CedarGroveStudios/Robot_Friend_FeatherWing/code/RobotFriend_tiny.bmp

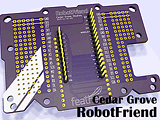
code/RobotFriend_tiny.bmp
