CedarGroveStudios/Robot_Friend_FeatherWing/photos and graphics/9mm_board_spacers.jpg

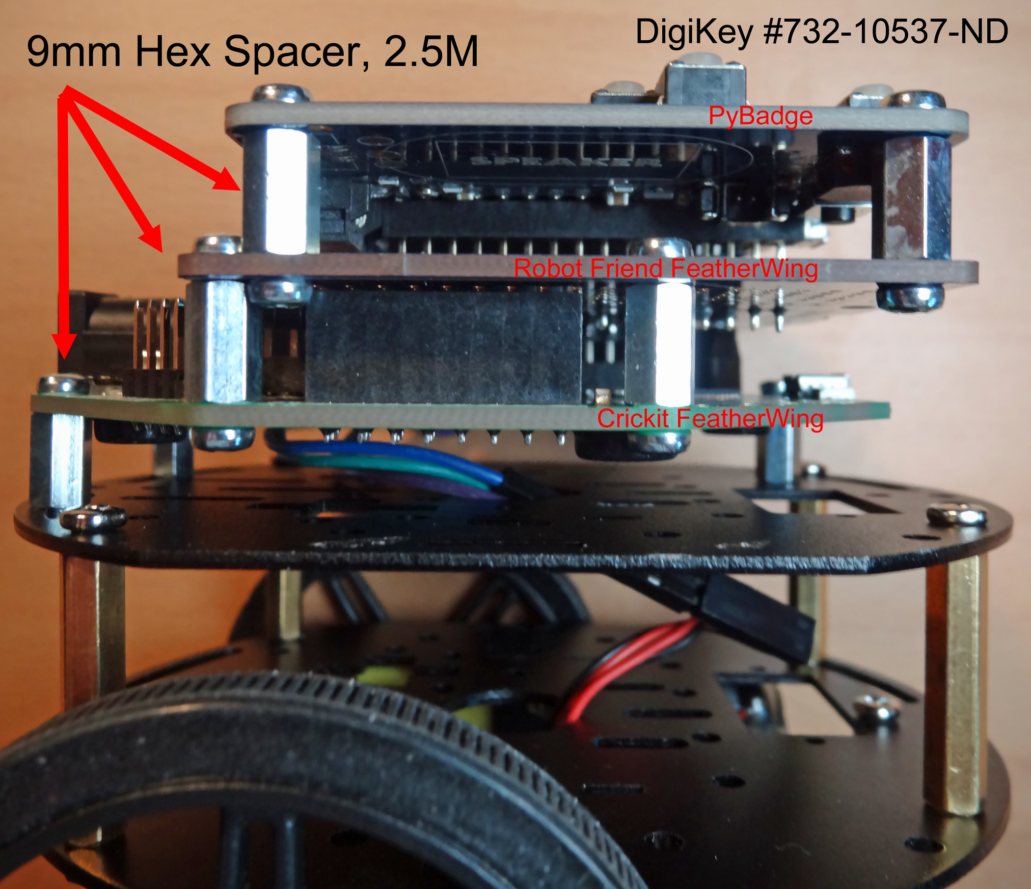
photos and graphics/9mm_board_spacers.jpg
