CedarGroveStudios/Robot_Friend_FeatherWing/photos and graphics/9mm_board_spacers_wide.jpg

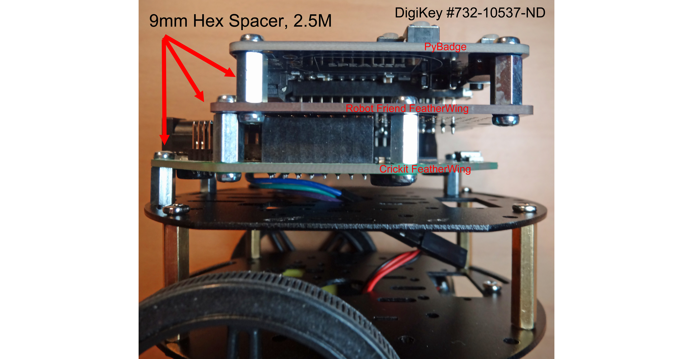
photos and graphics/9mm_board_spacers_wide.jpg
