CedarGroveStudios/Robot_Friend_FeatherWing/photos and graphics/2019-12-12_stemma_discovery.jpg

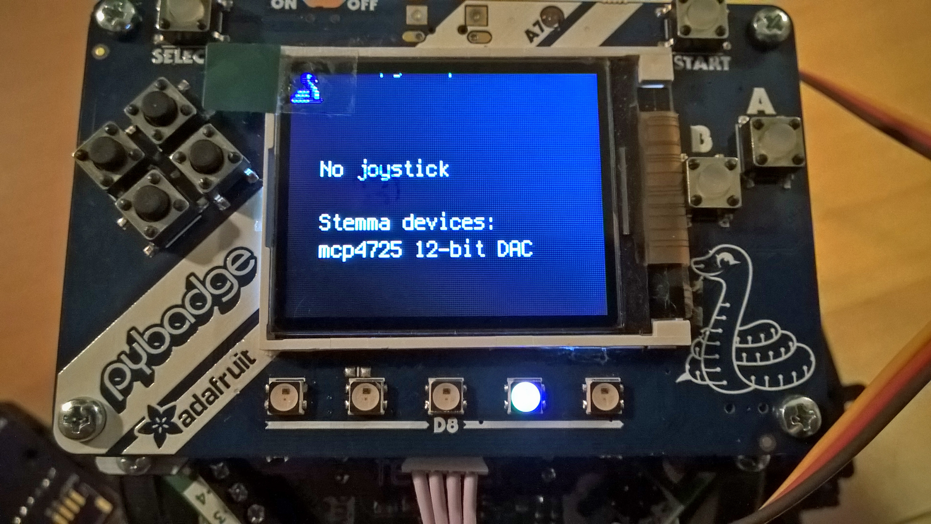
photos and graphics/2019-12-12_stemma_discovery.jpg
