CedarGroveStudios/Robot_Friend_FeatherWing/photos and graphics/Crickit_audio_jumper.jpg

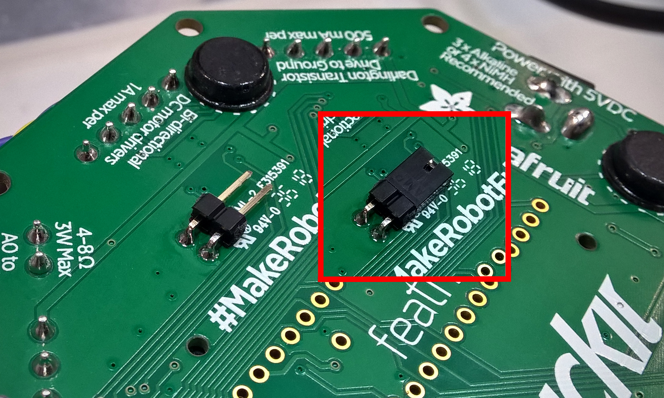
photos and graphics/Crickit_audio_jumper.jpg
