CedarGroveStudios/Robot_Friend_FeatherWing/photos and graphics/DSC05847a.jpg

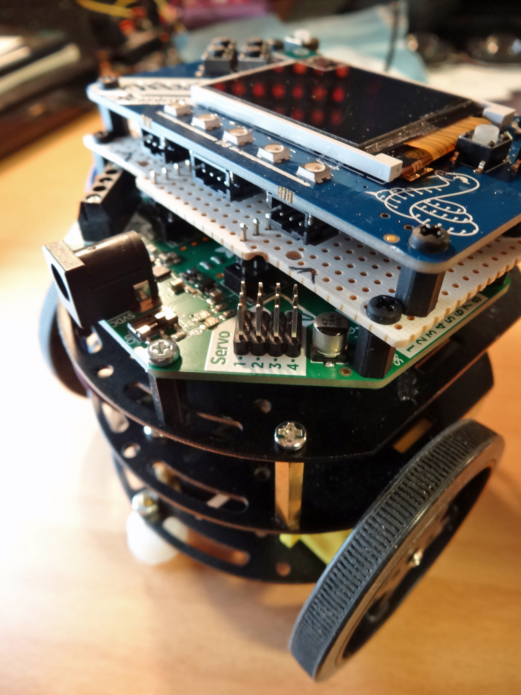
photos and graphics/DSC05847a.jpg
