CedarGroveStudios/Robot_Friend_FeatherWing/photos and graphics/DSC05849a.jpg

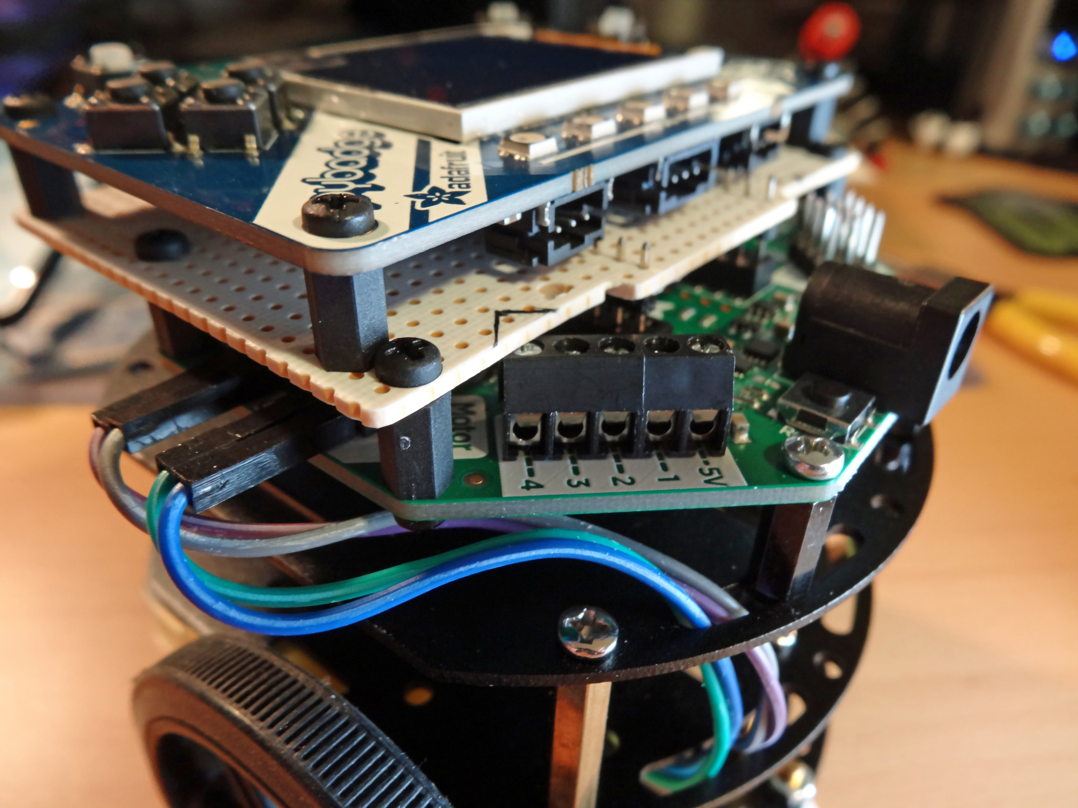
photos and graphics/DSC05849a.jpg
