CedarGroveStudios/Robot_Friend_FeatherWing/photos and graphics/DSC05850a.jpg

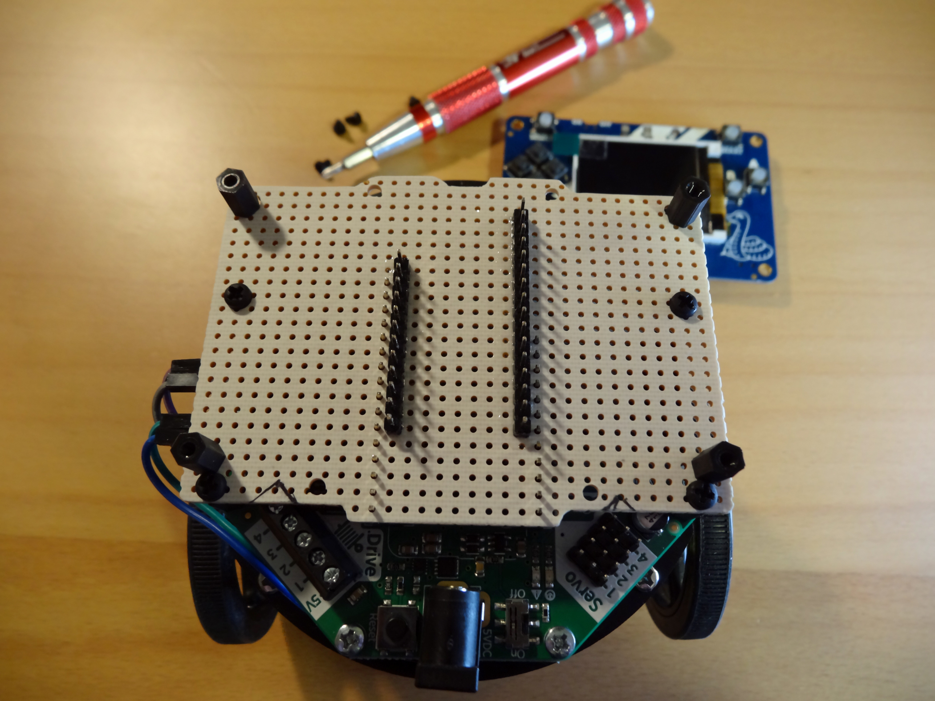
photos and graphics/DSC05850a.jpg
