CedarGroveStudios/Robot_Friend_FeatherWing/photos and graphics/DSC05886a.jpg

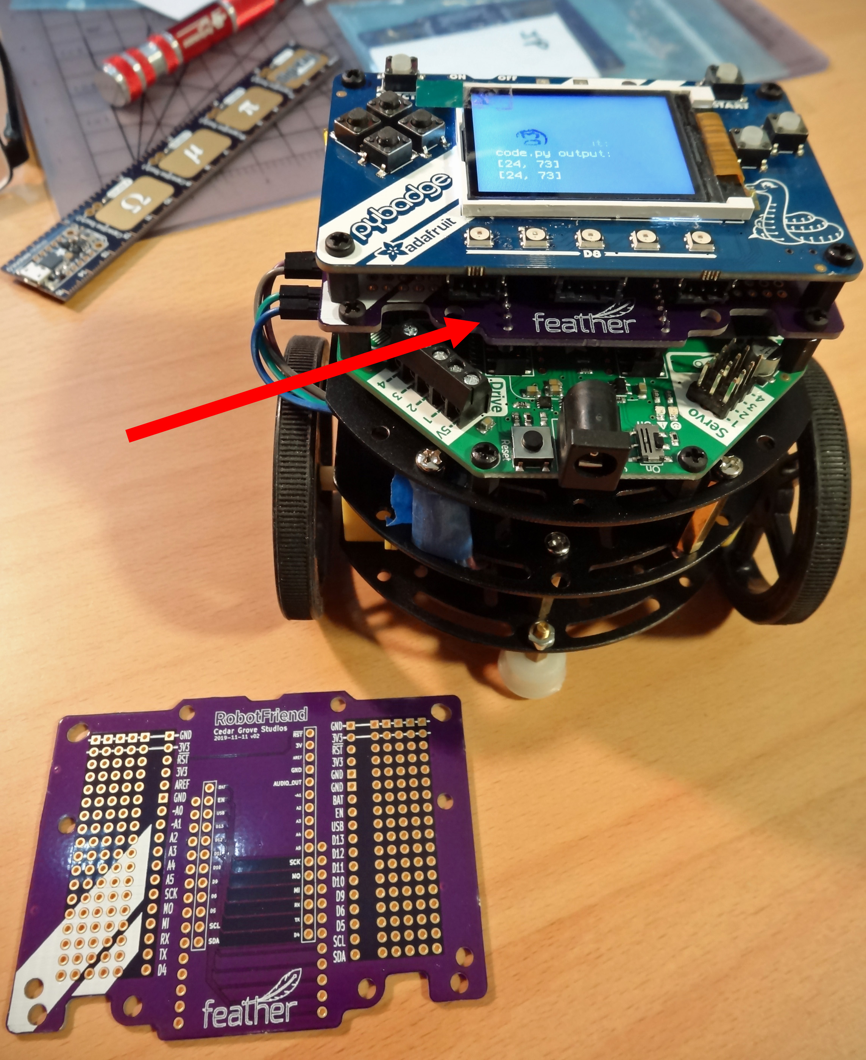
photos and graphics/DSC05886a.jpg
