CedarGroveStudios/Robot_Friend_FeatherWing/photos and graphics/DSC05920a lores.jpg

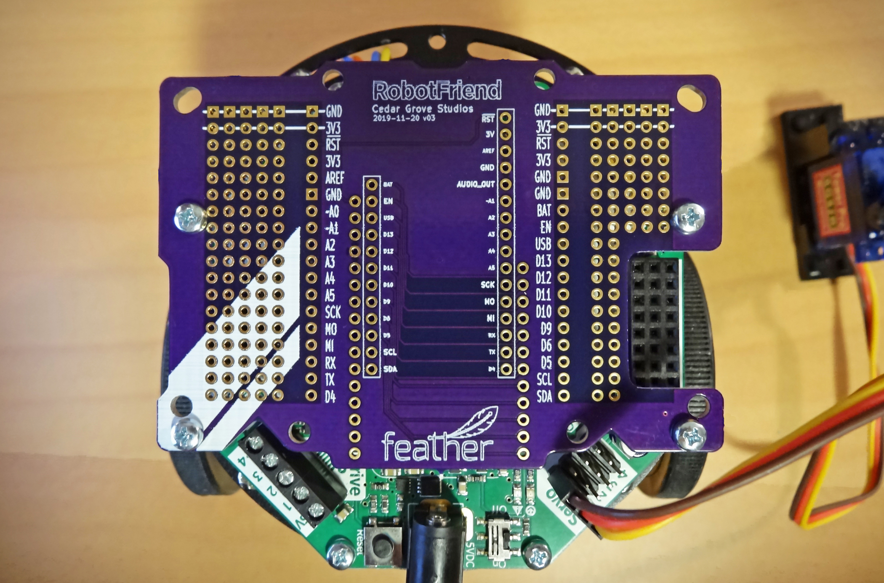
photos and graphics/DSC05920a lores.jpg
