CedarGroveStudios/Robot_Friend_FeatherWing/photos and graphics/musique concrete/DSC05933.JPG

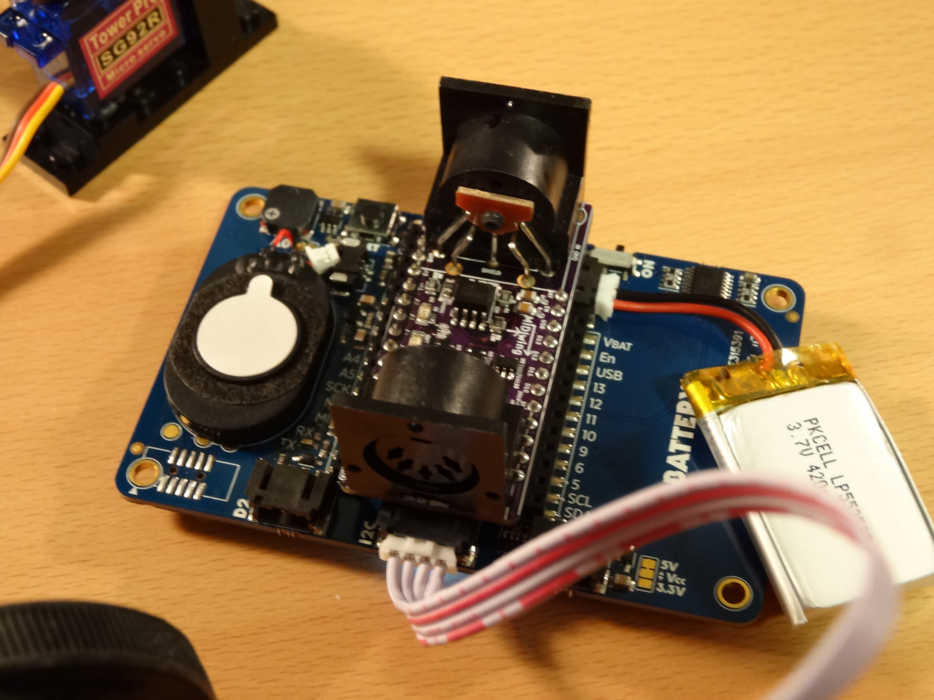
photos and graphics/musique concrete/DSC05933.JPG
