CedarGroveStudios/Robot_Friend_FeatherWing/photos and graphics/musique concrete/DSC05933a.jpg

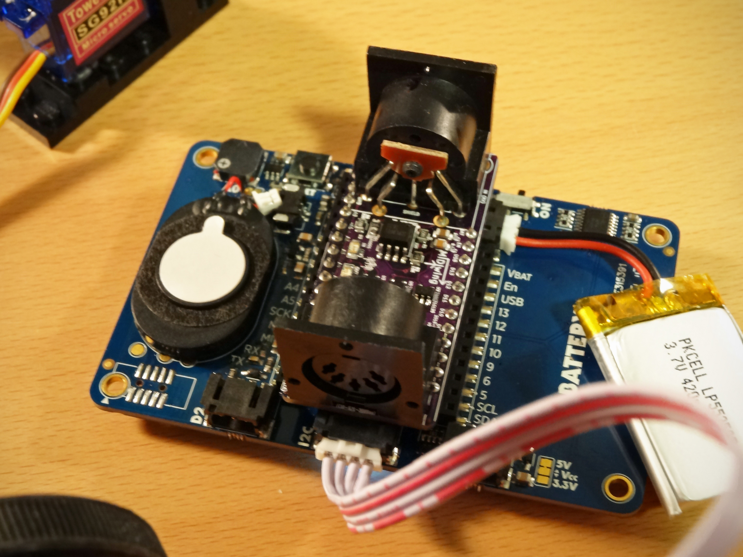
photos and graphics/musique concrete/DSC05933a.jpg
