CedarGroveStudios/Robot_Friend_FeatherWing/photos and graphics/musique concrete/DSC05934.JPG

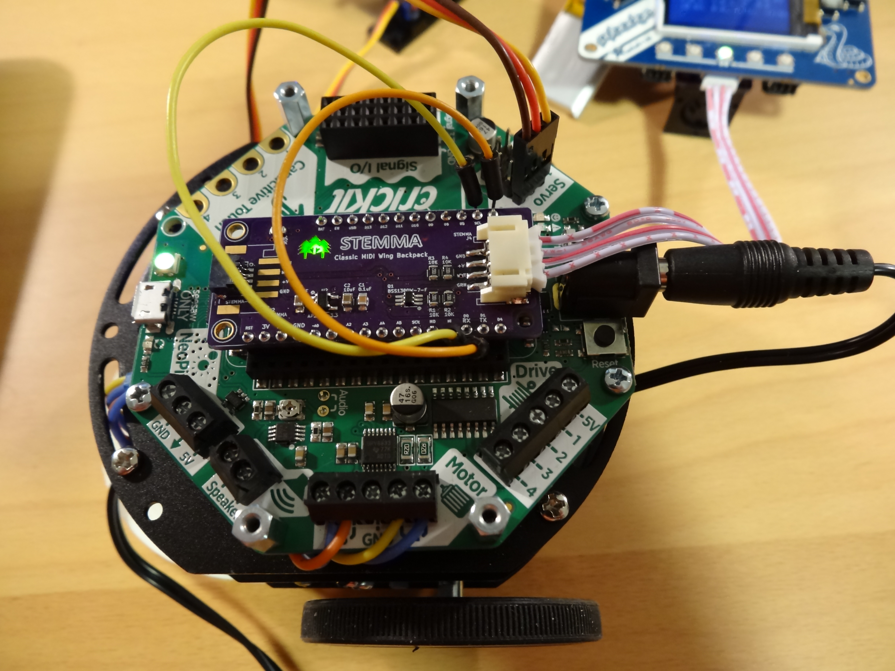
photos and graphics/musique concrete/DSC05934.JPG
