CedarGroveStudios/Robot_Friend_FeatherWing/photos and graphics/musique concrete/DSC05934a.jpg

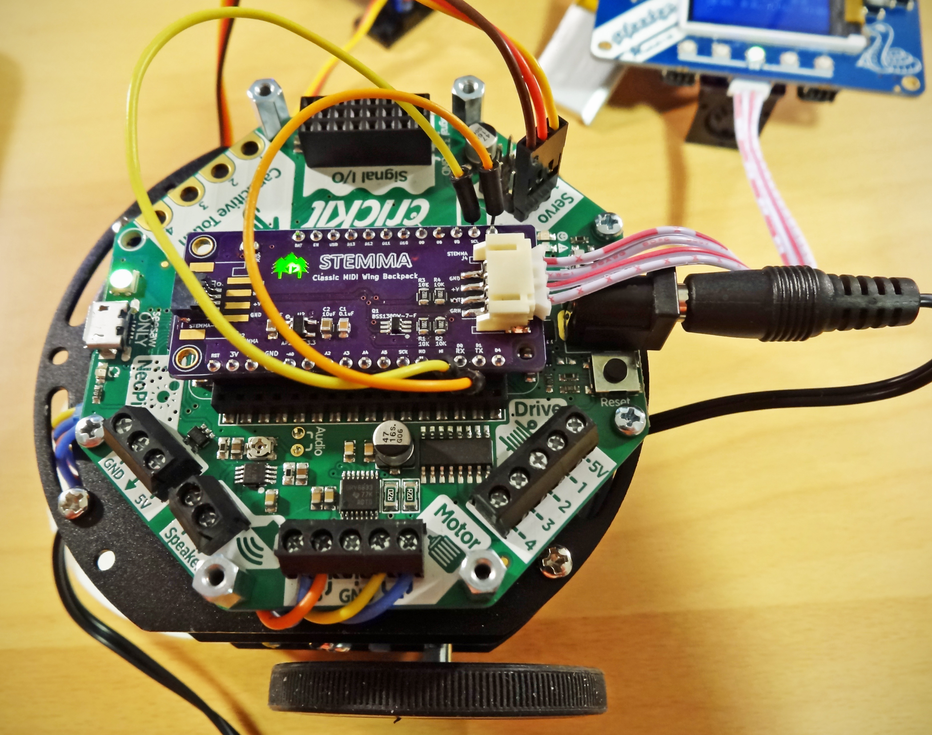
photos and graphics/musique concrete/DSC05934a.jpg
