CedarGroveStudios/Robot_Friend_FeatherWing/photos and graphics/RF_with_HolloWing.jpg

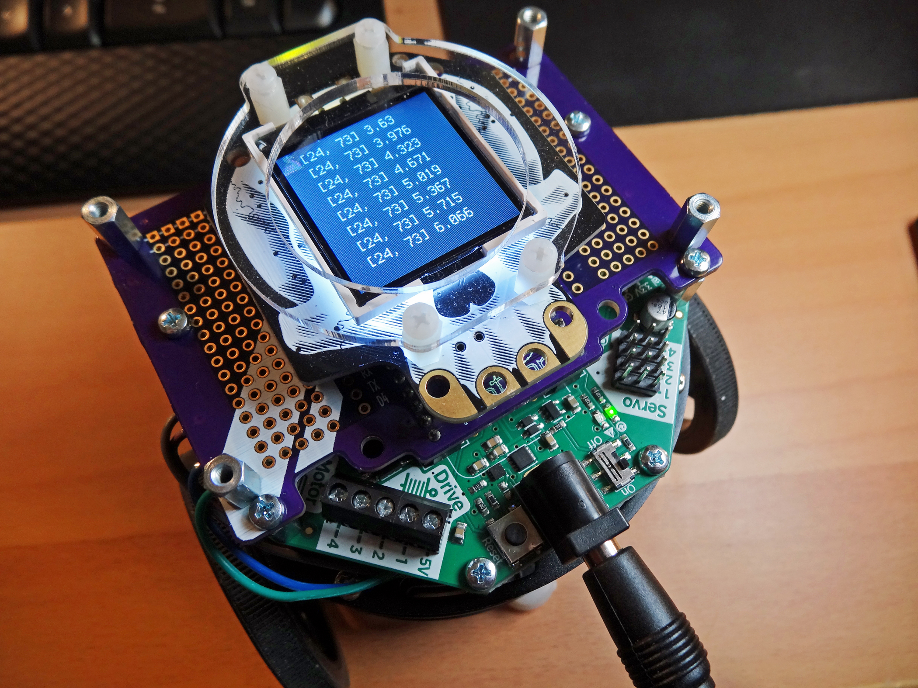
photos and graphics/RF_with_HolloWing.jpg
