CedarGroveStudios/Robot_Friend_FeatherWing/photos and graphics/Robot_Friend_bot_square.png

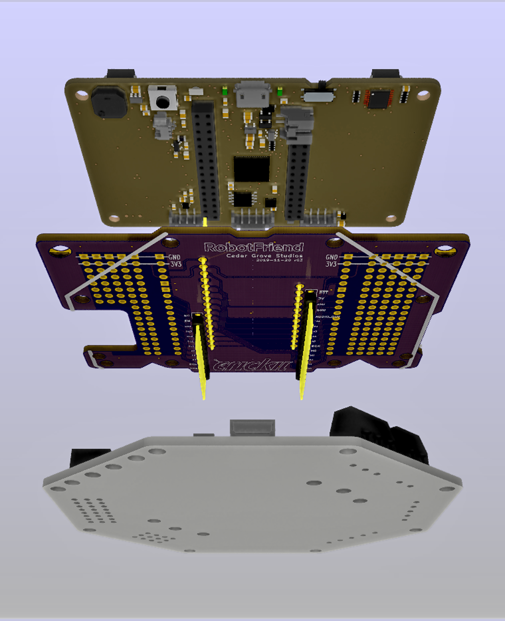
photos and graphics/Robot_Friend_bot_square.png
