CedarGroveStudios/Robot_Friend_FeatherWing/photos and graphics/Robot_Friend_expl.png

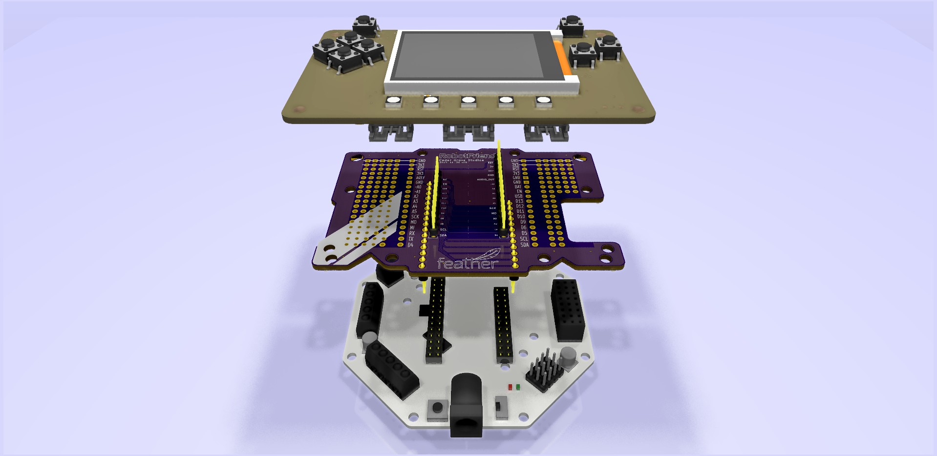
photos and graphics/Robot_Friend_expl.png
