CedarGroveStudios/Robot_Friend_FeatherWing/photos and graphics/Robot_Friend_expl_square.png

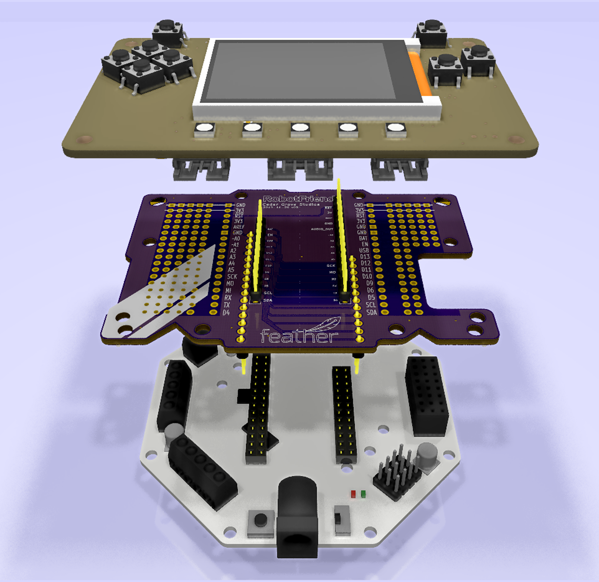
photos and graphics/Robot_Friend_expl_square.png
