CedarGroveStudios/Robot_Friend_FeatherWing/photos and graphics/Robot_Friend_glam.png

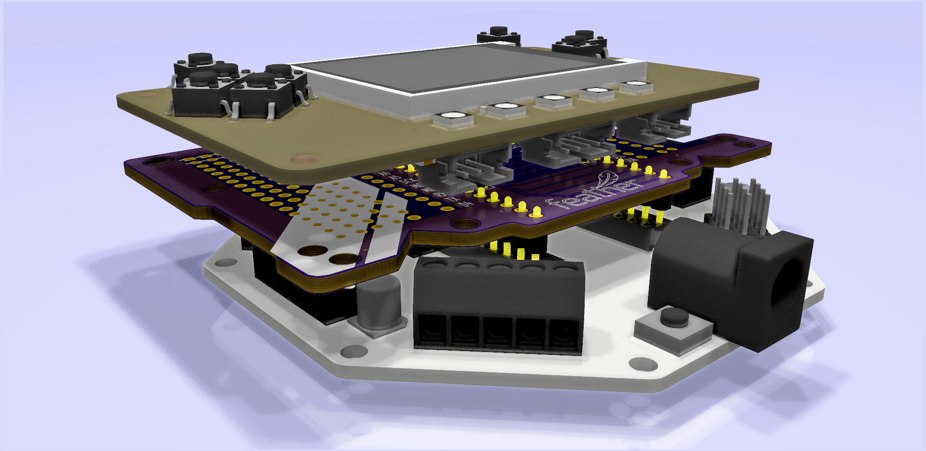
photos and graphics/Robot_Friend_glam.png
