CedarGroveStudios/Robot_Friend_FeatherWing/photos and graphics/Robot_Friend_PCB_edge.png

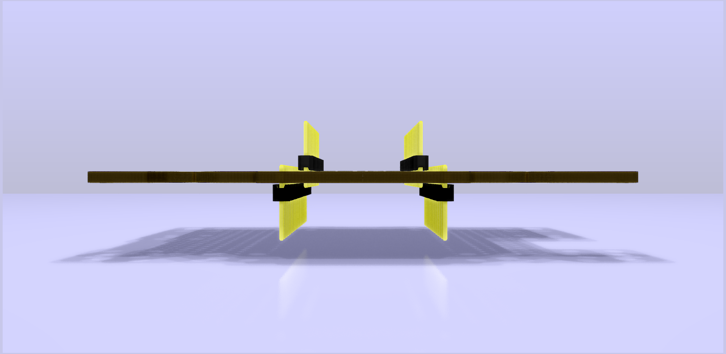
photos and graphics/Robot_Friend_PCB_edge.png
