CedarGroveStudios/Robot_Friend_FeatherWing/photos and graphics/Robot_Friend_PCB_glam.png

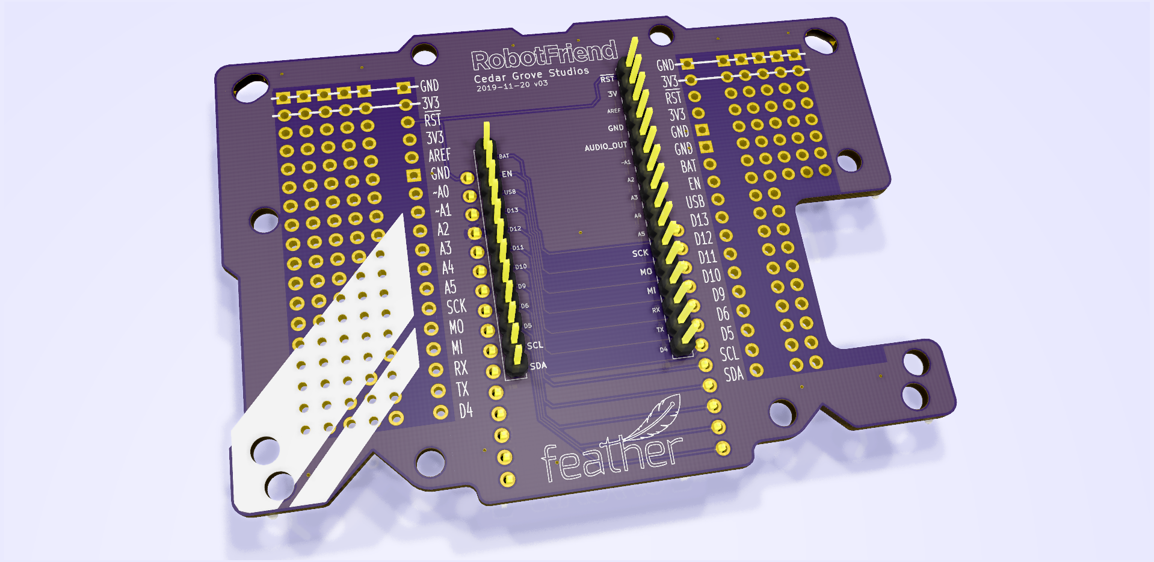
photos and graphics/Robot_Friend_PCB_glam.png
