CedarGroveStudios/Robot_Friend_FeatherWing/photos and graphics/PB_PG_test_combo.jpg

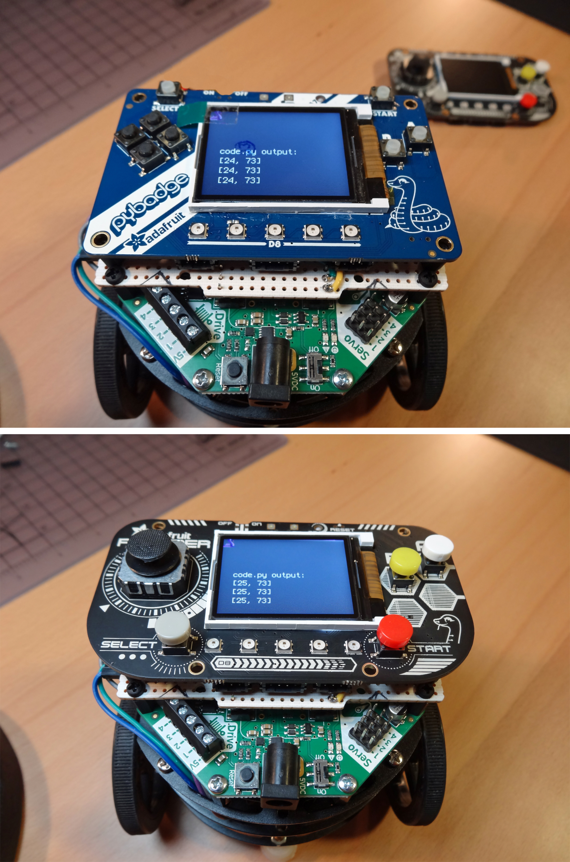
photos and graphics/PB_PG_test_combo.jpg
